piro-s/generator/program/generator_v2/Core/inc/mcp4728.h

/*
 * @file mcp4728.h
 *
 * Lib for MCP4728
 *
 * @Created on: 05.04.2021 15:10:52
 * @Author: piro.tex
 */

#ifndef __mcp4728_h__
#define __mcp4728_h__


///--- #include
#include "stm32f1xx.h"


///--- initializations


///--- handlers


///--- functions


///--- setters/getters


///--- enum's


///--- struct


///--- constants


///--- varibles


///--- variables struct


///--- counters


///--- flags

#endif
