piro-s/generator/program/generator_v2/Core/src/mcp4728.c

/*
 * @file mcp4728.c
 *
 * @Created on: 05.04.2021 15:11:08
 * @Author: piro.tex
 */


///--- #include
#include "../inc/mcp4728.h"
#include "../inc/tools.h"


///--- struct


///--- constants


///--- varibles


///--- variables struct


///--- counters


///--- flags


///--- initializations


///--- handlers


///--- functions


///--- setters/getters


///--- enum's
